RavingRoss/ALMA/Documentation/IGNITE/IGNITE_ALMA.pdf

## 12 Results from Prior Support

There is no prior results because ALMA is a new project. The team has done research on FBLs about

how the physics works, the amplification inside the fiber cable, why to use a FBL and not a different type,

the mining techniques to be used, and the effects of lASERs in space.

9
