RavingRoss/ALMA/Fall 23/Results/aberration-plot.png

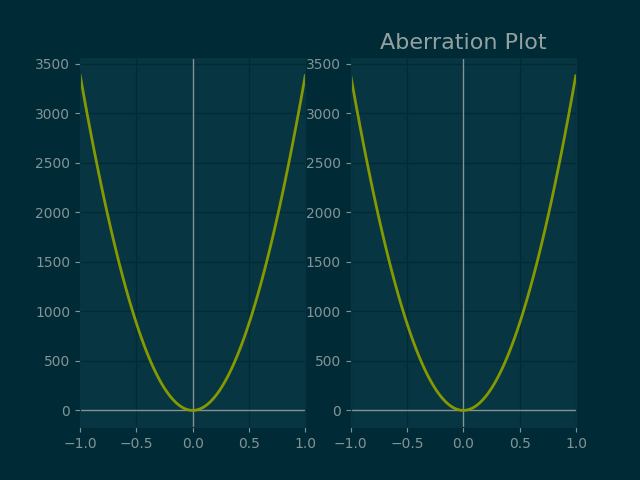
Fall 23/Results/aberration-plot.png
