RavingRoss/ALMA/Fall 23/Results/JacobAlisaDivyeshwari_RomeoTiselskaVansadia-Gr8_Sec1_Prism_Info.png

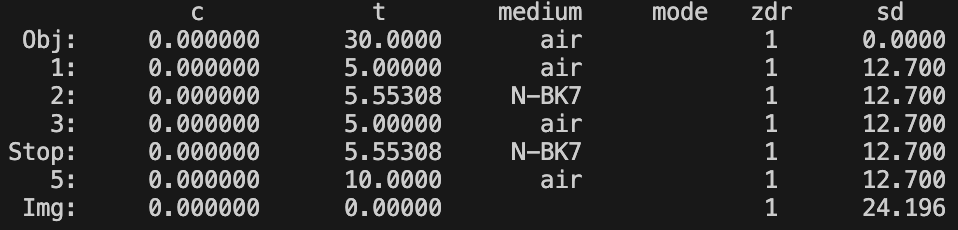
Fall 23/Results/JacobAlisaDivyeshwari_RomeoTiselskaVansadia-Gr8_Sec1_Prism_Info.png
