RavingRoss/ALMA/Fall 23/Results/JacobAlisaDivyeshwari_RomeoTiselskaVansadia-Gr8_Sec1_Ray_Diagram.png

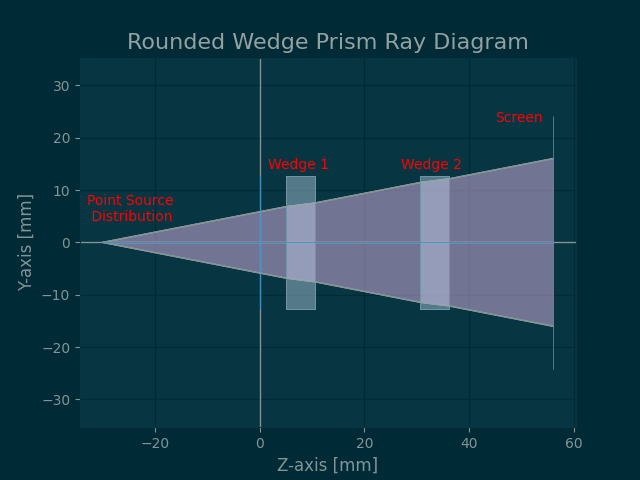
Fall 23/Results/JacobAlisaDivyeshwari_RomeoTiselskaVansadia-Gr8_Sec1_Ray_Diagram.png
