RavingRoss/ALMA/Documentation/Manuals/seed-diode.pdf

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

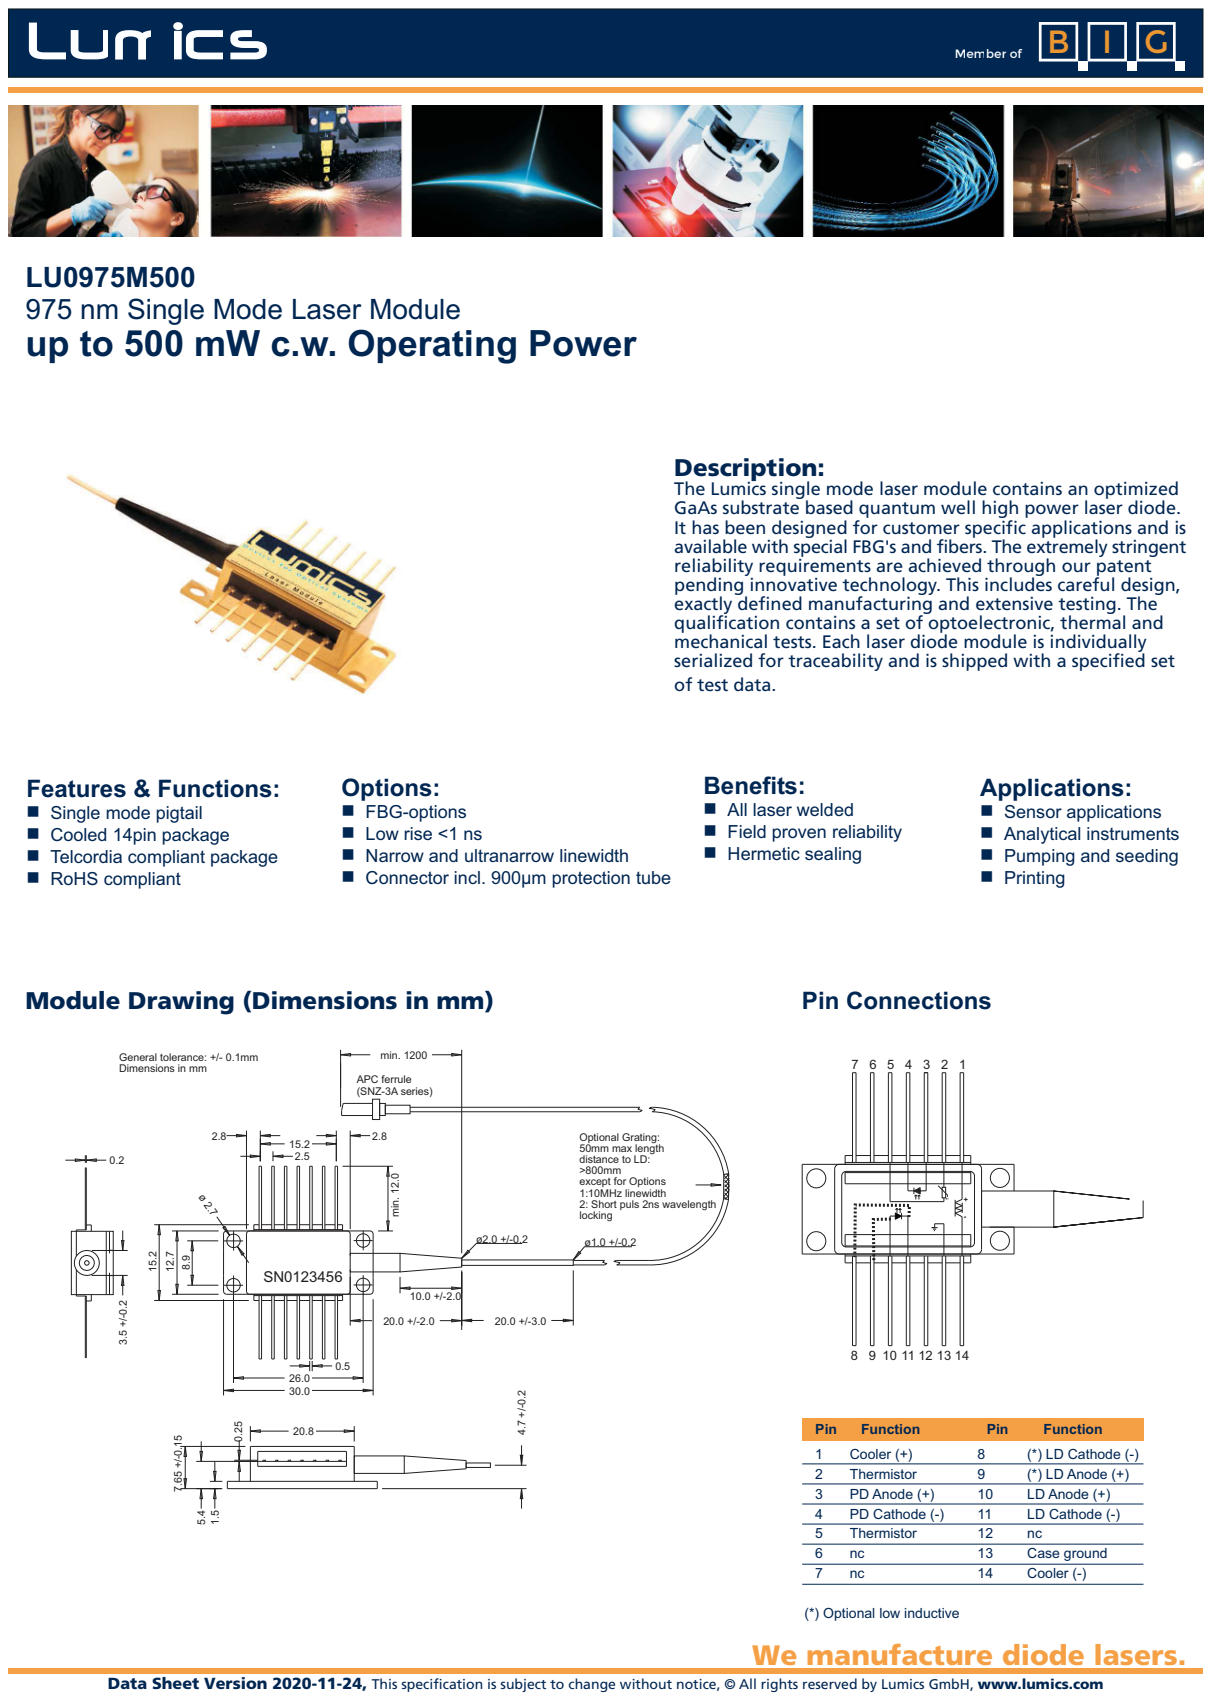
[picture p25: page 1]

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
